ymz000/ItsyBitsyBreadboardAdapter/photos/adapter combo lores.jpg

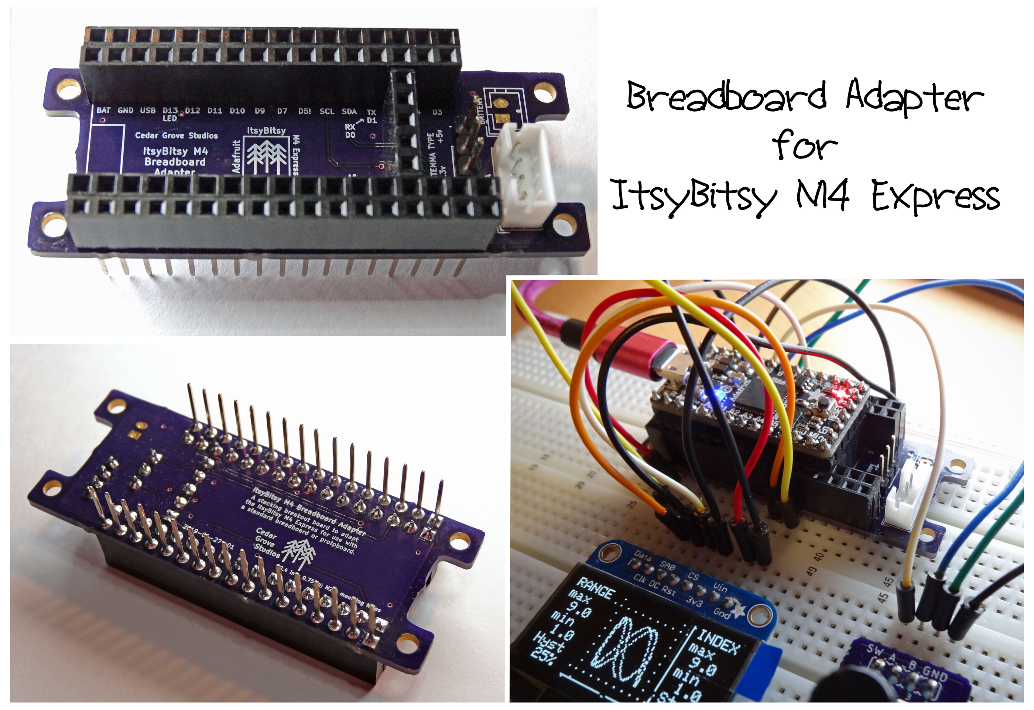
photos/adapter combo lores.jpg
