ymz000/ItsyBitsyBreadboardAdapter/photos/DSC05935a.jpg

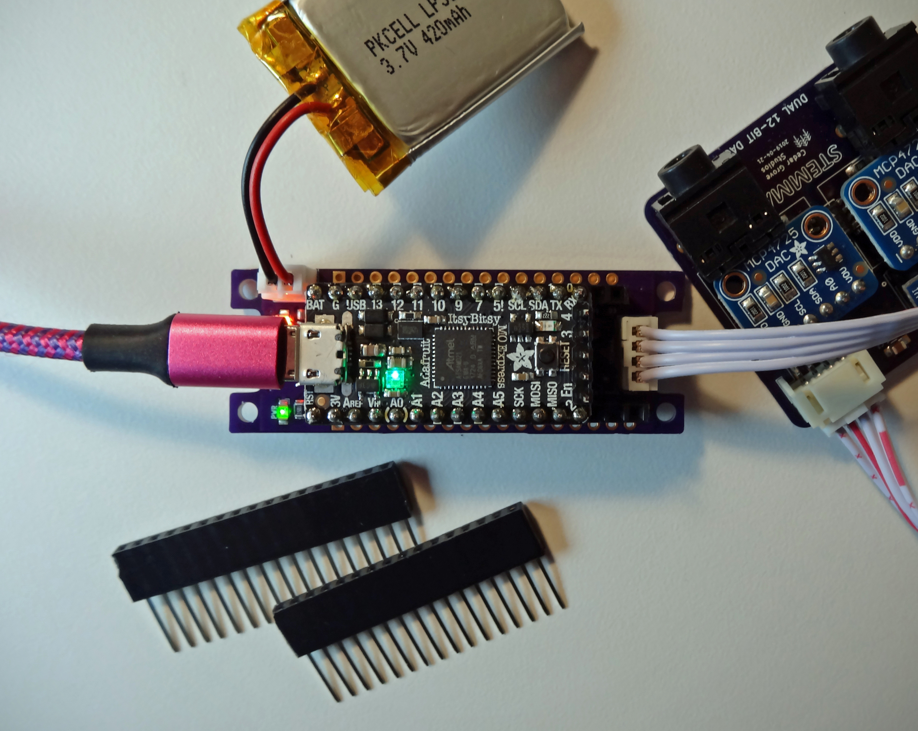
photos/DSC05935a.jpg
