ymz000/ItsyBitsyBreadboardAdapter/photos/ItsyBitsy breadboard stemma.png

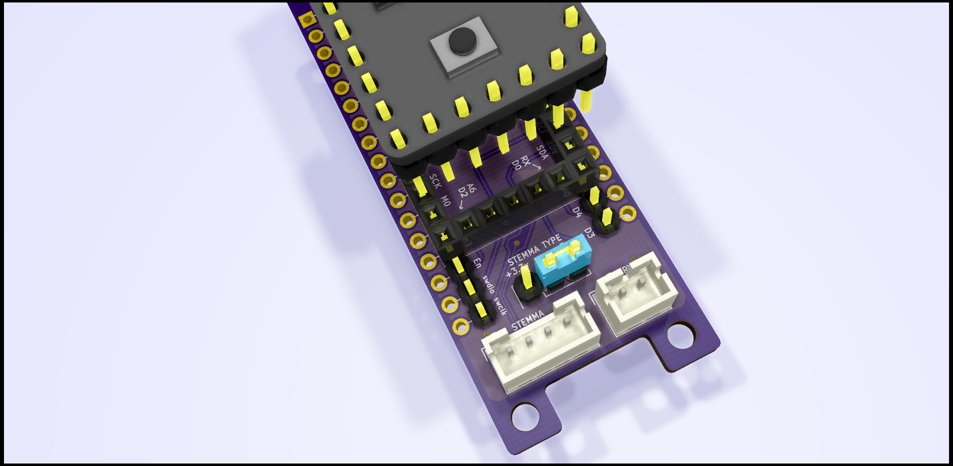
photos/ItsyBitsy breadboard stemma.png
