ymz000/ItsyBitsyBreadboardAdapter/photos/ItsyBitsy breadboard.png

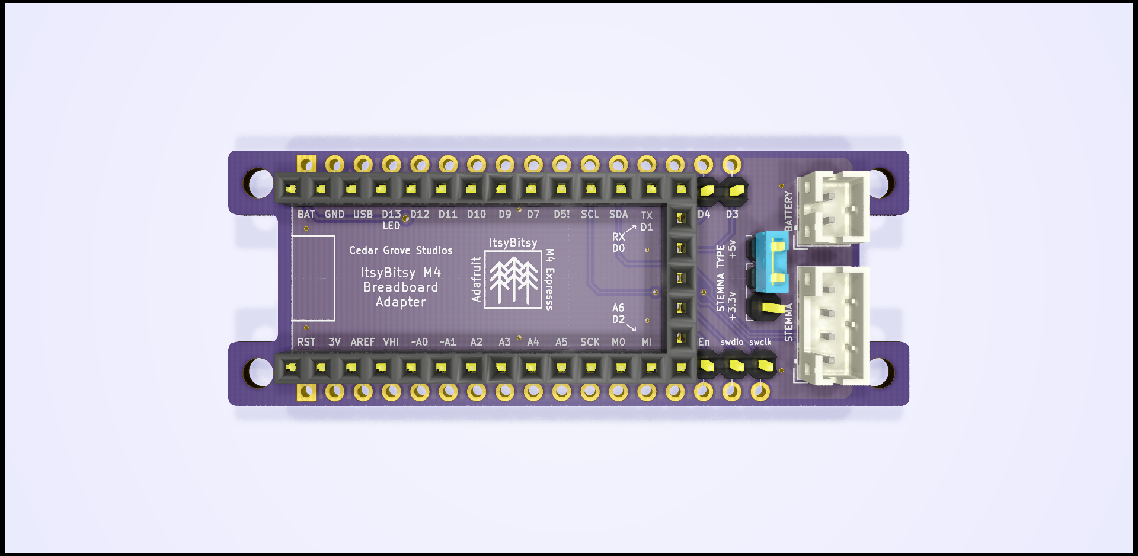
photos/ItsyBitsy breadboard.png
