ymz000/ItsyBitsyBreadboardAdapter/photos/ItsyBitsy_breadboard.png

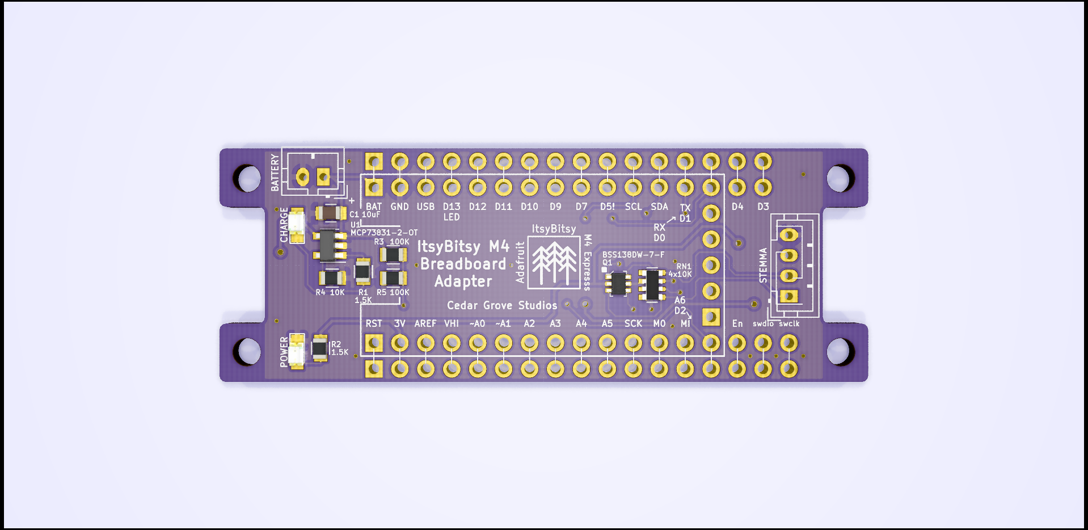
photos/ItsyBitsy_breadboard.png
