ymz000/ItsyBitsyBreadboardAdapter/photos/ItsyBitsy_breadboard_glam.png

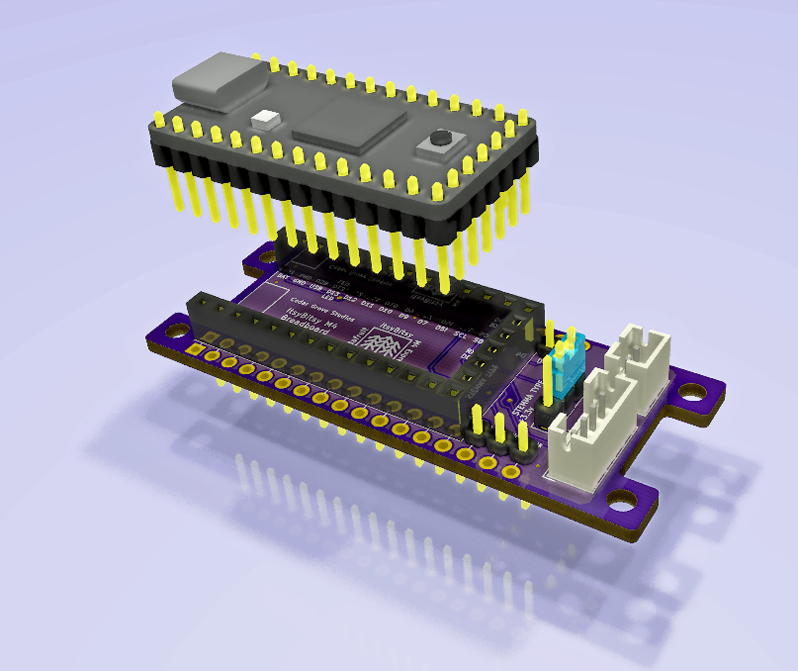
photos/ItsyBitsy_breadboard_glam.png
