ymz000/ItsyBitsyBreadboardAdapter/photos/ItsyBitsy_breadboard_glam_hover.png

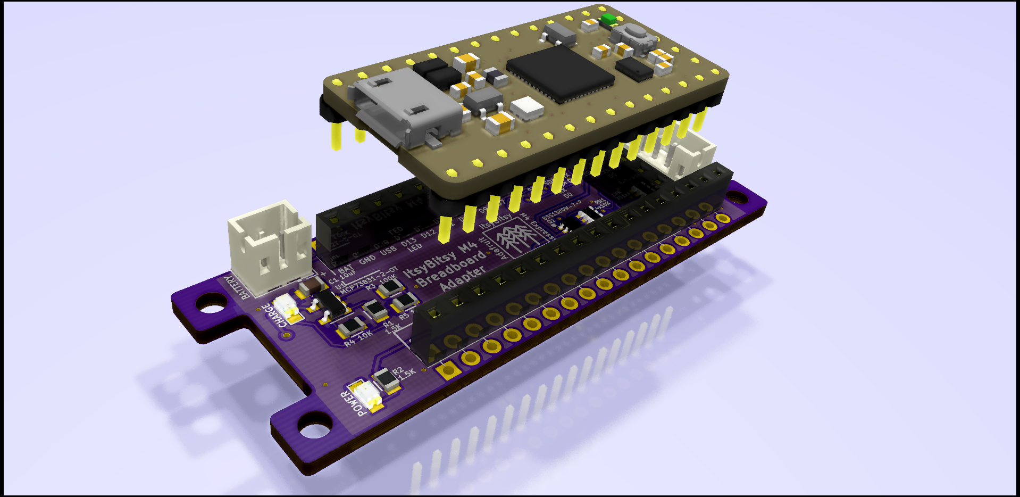
photos/ItsyBitsy_breadboard_glam_hover.png
