ymz000/ItsyBitsyBreadboardAdapter/photos/ItsyBitsy_breadboard_glam_stemma.png

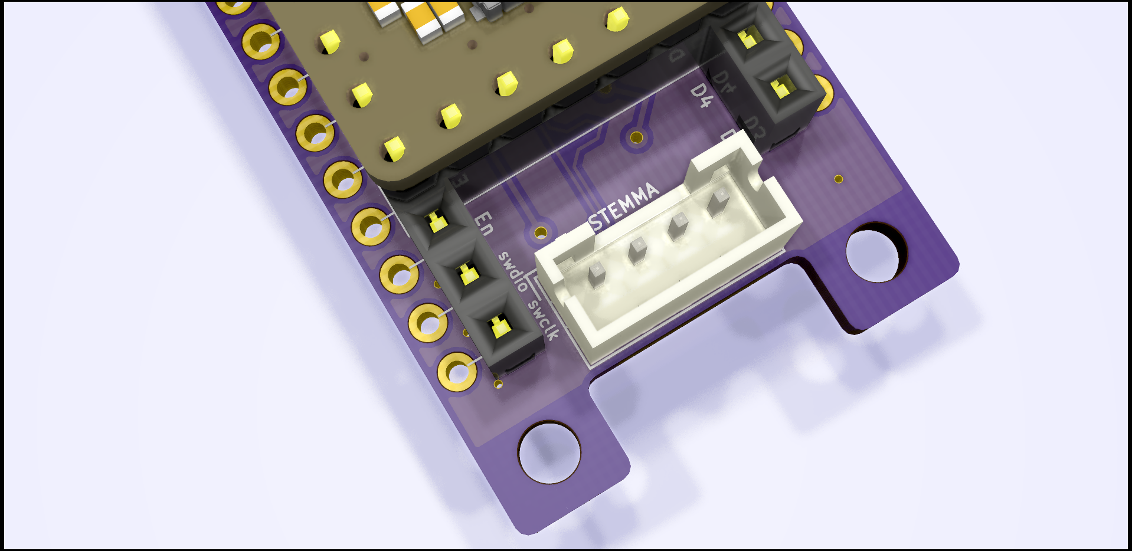
photos/ItsyBitsy_breadboard_glam_stemma.png
