ymz000/ItsyBitsyBreadboardAdapter/photos/ItsyBitsy_breadboard_PCB_combo.png

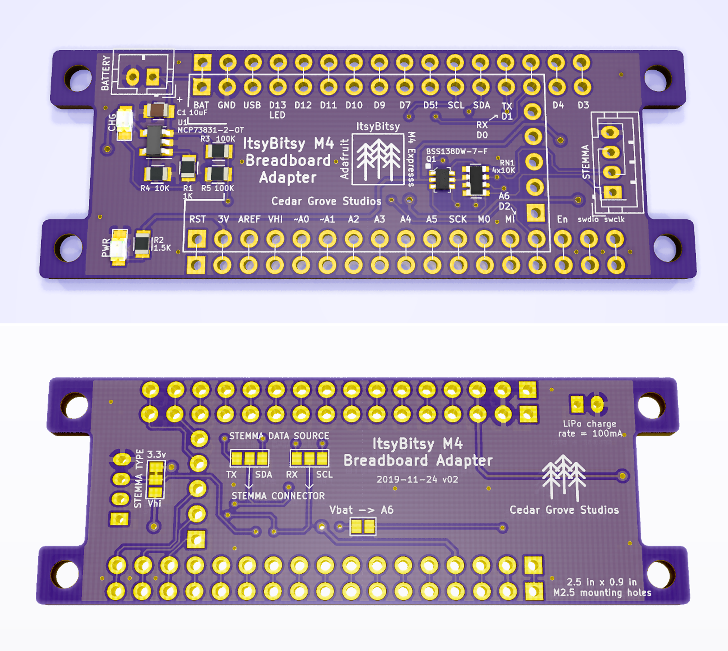
photos/ItsyBitsy_breadboard_PCB_combo.png
