ymz000/ItsyBitsyBreadboardAdapter/photos/ItsyBitsy_breadboard_stack_glam.png

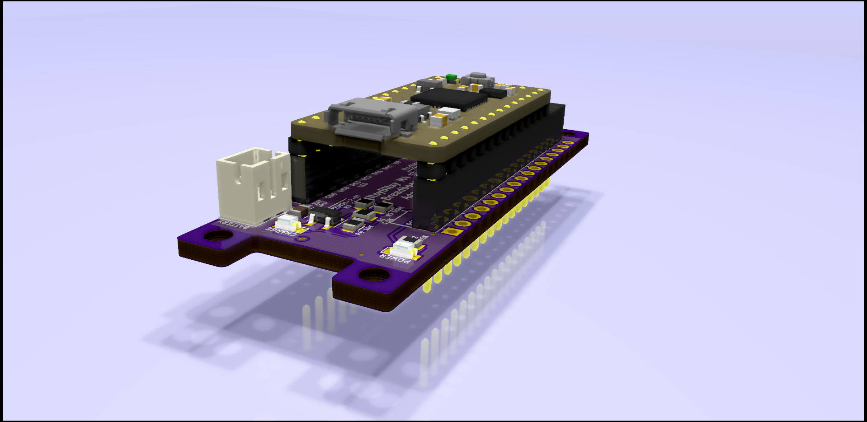
photos/ItsyBitsy_breadboard_stack_glam.png
