ymz000/ItsyBitsyBreadboardAdapter/photos/pygamer batt mgt.png

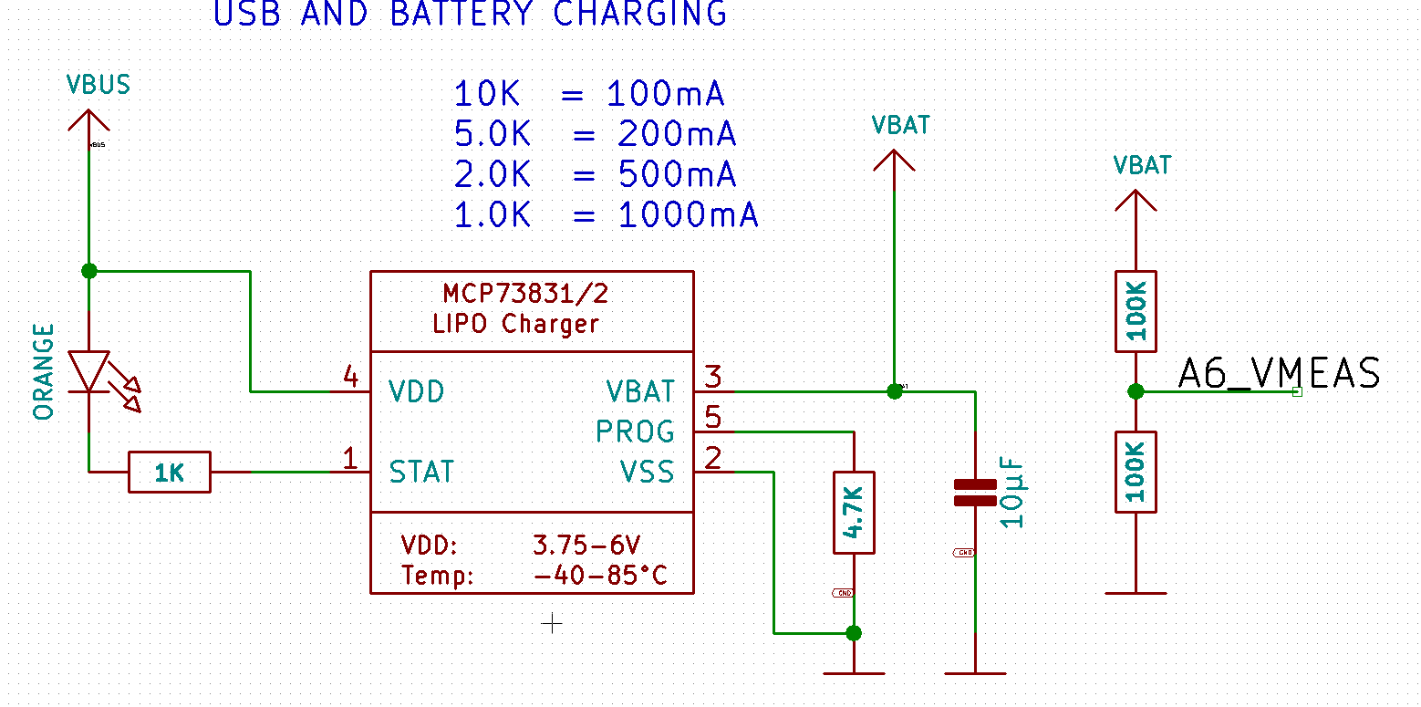
photos/pygamer batt mgt.png
