ymz000/ItsyBitsyBreadboardAdapter/photos/pygamer power management.png

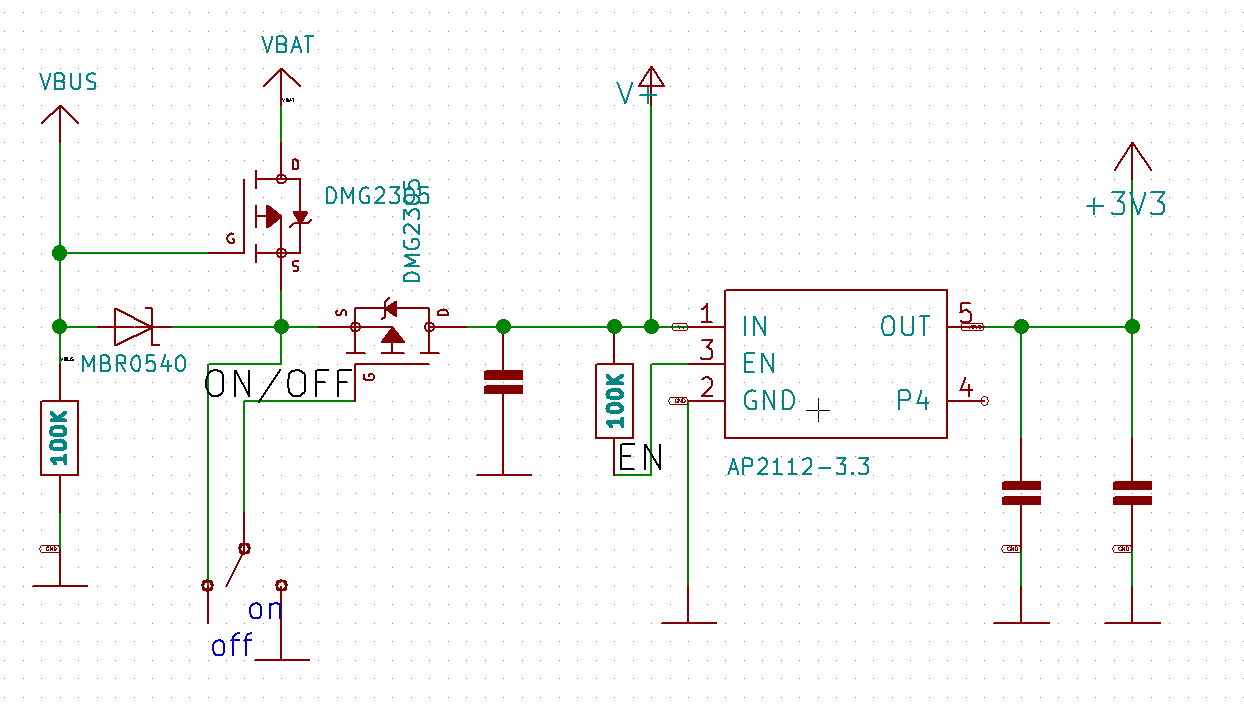
photos/pygamer power management.png
