ymz000/ItsyBitsyBreadboardAdapter/photos/RoverWing charger circuit.jpg

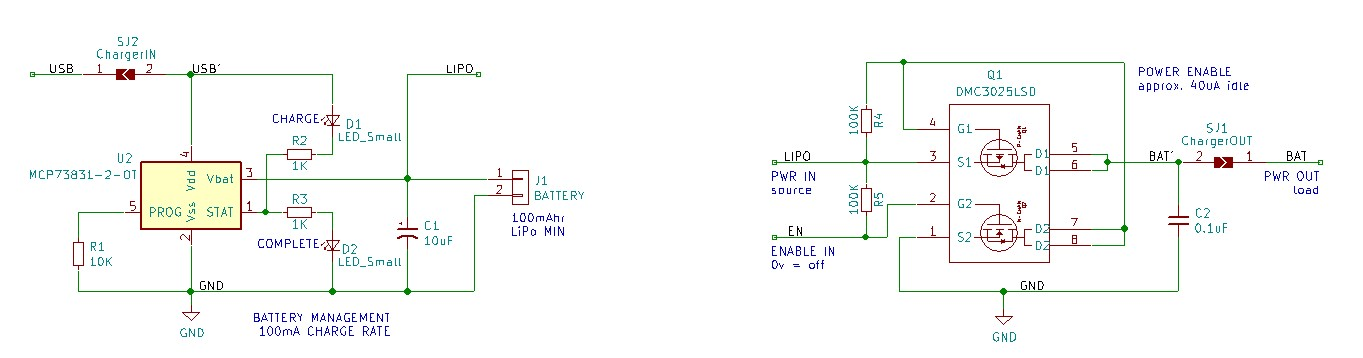
photos/RoverWing charger circuit.jpg
