ymz000/ItsyBitsyBreadboardAdapter/photos/swd connector.jpg

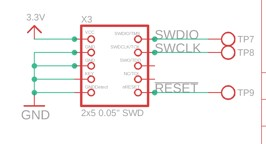
photos/swd connector.jpg
